benlucy/Arduino-Portable-Portrait-Painter/LiveOV7670/BufferedCameraOV7670_QQVGA_20hz_Grayscale.h

//
// Created by indrek on 30.04.2016.
//

#ifndef _BUFFEREDCAMERAOV7670_QQVGA_20HZ_GRAYSCALE_H
#define _BUFFEREDCAMERAOV7670_QQVGA_20HZ_GRAYSCALE_H

#include "BufferedCameraOV7670.h"


// 160 x 120 @ 10Hz
class BufferedCameraOV7670_QQVGA_20hz_Grayscale : public BufferedCameraOV7670<uint8_t, 160, uint8_t, 160, uint8_t, 120> {

public:
    BufferedCameraOV7670_QQVGA_20hz_Grayscale() : BufferedCameraOV7670(RESOLUTION_QQVGA_160x120, PIXEL_YUV422, 1, PLL_MULTIPLIER_X4) {};

    inline void readLine() override __attribute__((always_inline));
    void isrReadLine();

protected:
    bool setUpCamera() override;

private:
    inline void readPixels_unrolled_x160(uint16_t byteIndex) __attribute__((always_inline));
    inline void readPixels_unrolled_x10(uint16_t byteIndex) __attribute__((always_inline));
    inline void readPixel_unrolled(uint16_t byteIndex) __attribute__((always_inline));

};


volatile bool isrRead = false;
BufferedCameraOV7670_QQVGA_20hz_Grayscale * isrCamera = nullptr;



bool BufferedCameraOV7670_QQVGA_20hz_Grayscale::setUpCamera() {
  if (CameraOV7670::setUpCamera()) {
    isrCamera = this;

    *digitalPinToPCMSK(OV7670_PIXEL_CLOCK_PIN) |= bit (digitalPinToPCMSKbit(OV7670_PIXEL_CLOCK_PIN));  // enable pin
    PCICR  = 0; // disable interrupt

    return true;
  } else {
    return false;
  }
}




ISR (PCINT0_vect) { // handle pin change interrupt for D8 to D13 here
  isrCamera->isrReadLine();
  PCICR  = 0; // disable interrupt
  isrRead = false;
}


void BufferedCameraOV7670_QQVGA_20hz_Grayscale::readLine() {
  isrRead = true;
  PCIFR  |= bit(digitalPinToPCICRbit(OV7670_PIXEL_CLOCK_PIN)); // clear any outstanding interrupt
  PCICR  |= bit(digitalPinToPCICRbit(OV7670_PIXEL_CLOCK_PIN)); // enable interrupt for the group
  pixelBuffer.writeBufferPadding = 0;
  while(isrRead);
}



void BufferedCameraOV7670_QQVGA_20hz_Grayscale::isrReadLine() {
  asm volatile("nop");
  asm volatile("nop");

  // only way to get line data at 20Hz is to unroll pixel reading
  readPixels_unrolled_x160(0);
}


#define BufferedCameraOV7670_QQVGA_20hz_Grayscale_READ_PIXEL_X160_STEP 10
void BufferedCameraOV7670_QQVGA_20hz_Grayscale::readPixels_unrolled_x160(uint16_t byteIndex) {
  readPixels_unrolled_x10(byteIndex + BufferedCameraOV7670_QQVGA_20hz_Grayscale_READ_PIXEL_X160_STEP * 0);
  readPixels_unrolled_x10(byteIndex + BufferedCameraOV7670_QQVGA_20hz_Grayscale_READ_PIXEL_X160_STEP * 1);
  readPixels_unrolled_x10(byteIndex + BufferedCameraOV7670_QQVGA_20hz_Grayscale_READ_PIXEL_X160_STEP * 2);
  readPixels_unrolled_x10(byteIndex + BufferedCameraOV7670_QQVGA_20hz_Grayscale_READ_PIXEL_X160_STEP * 3);
  readPixels_unrolled_x10(byteIndex + BufferedCameraOV7670_QQVGA_20hz_Grayscale_READ_PIXEL_X160_STEP * 4);
  readPixels_unrolled_x10(byteIndex + BufferedCameraOV7670_QQVGA_20hz_Grayscale_READ_PIXEL_X160_STEP * 5);
  readPixels_unrolled_x10(byteIndex + BufferedCameraOV7670_QQVGA_20hz_Grayscale_READ_PIXEL_X160_STEP * 6);
  readPixels_unrolled_x10(byteIndex + BufferedCameraOV7670_QQVGA_20hz_Grayscale_READ_PIXEL_X160_STEP * 7);
  readPixels_unrolled_x10(byteIndex + BufferedCameraOV7670_QQVGA_20hz_Grayscale_READ_PIXEL_X160_STEP * 8);
  readPixels_unrolled_x10(byteIndex + BufferedCameraOV7670_QQVGA_20hz_Grayscale_READ_PIXEL_X160_STEP * 9);
  readPixels_unrolled_x10(byteIndex + BufferedCameraOV7670_QQVGA_20hz_Grayscale_READ_PIXEL_X160_STEP * 10);
  readPixels_unrolled_x10(byteIndex + BufferedCameraOV7670_QQVGA_20hz_Grayscale_READ_PIXEL_X160_STEP * 11);
  readPixels_unrolled_x10(byteIndex + BufferedCameraOV7670_QQVGA_20hz_Grayscale_READ_PIXEL_X160_STEP * 12);
  readPixels_unrolled_x10(byteIndex + BufferedCameraOV7670_QQVGA_20hz_Grayscale_READ_PIXEL_X160_STEP * 13);
  readPixels_unrolled_x10(byteIndex + BufferedCameraOV7670_QQVGA_20hz_Grayscale_READ_PIXEL_X160_STEP * 14);
  readPixels_unrolled_x10(byteIndex + BufferedCameraOV7670_QQVGA_20hz_Grayscale_READ_PIXEL_X160_STEP * 15);
}


void BufferedCameraOV7670_QQVGA_20hz_Grayscale::readPixels_unrolled_x10(uint16_t byteIndex) {
  readPixel_unrolled(byteIndex + 0);
  readPixel_unrolled(byteIndex + 1);
  readPixel_unrolled(byteIndex + 2);
  readPixel_unrolled(byteIndex + 3);
  readPixel_unrolled(byteIndex + 4);
  readPixel_unrolled(byteIndex + 5);
  readPixel_unrolled(byteIndex + 6);
  readPixel_unrolled(byteIndex + 7);
  readPixel_unrolled(byteIndex + 8);
  readPixel_unrolled(byteIndex + 9);
}

void BufferedCameraOV7670_QQVGA_20hz_Grayscale::readPixel_unrolled(uint16_t byteIndex) {
  readPixelByte(pixelBuffer.writeBuffer[byteIndex]);
  asm volatile("nop");
}








#endif //_BUFFEREDCAMERAOV7670_QQVGA_20HZ_GRAYSCALE_H
