benlucy/Arduino-Portable-Portrait-Painter/LiveOV7670/GrayScaleTable.h

//
// Created by indrek on 1.12.2016.
//

#ifndef LIVEOV7670_GRAYSCALETABLE_H
#define LIVEOV7670_GRAYSCALETABLE_H




const uint8_t graysScaleTableHigh[] = {
    0x00,
    0x00,
    0x00,
    0x00,
    0x00,
    0x00,
    0x00,
    0x00,
    0x08,
    0x08,
    0x08,
    0x08,
    0x08,
    0x08,
    0x08,
    0x08,
    0x10,
    0x10,
    0x10,
    0x10,
    0x10,
    0x10,
    0x10,
    0x10,
    0x18,
    0x18,
    0x18,
    0x18,
    0x18,
    0x18,
    0x18,
    0x18,
    0x21,
    0x21,
    0x21,
    0x21,
    0x21,
    0x21,
    0x21,
    0x21,
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
};



uint8_t graysScaleTableLow[] = {
    0x00,
    0x00,
    0x00,
    0x00,
    0x20,
    0x20,
    0x20,
    0x20,
    0x41,
    0x41,
    0x41,
    0x41,
    0x61,
    0x61,
    0x61,
    0x61,
    0x82,
    0x82,
    0x82,
    0x82,
    0xA2,
    0xA2,
    0xA2,
    0xA2,
    0xC3,
    0xC3,
    0xC3,
    0xC3,
    0xE3,
    0xE3,
    0xE3,
    0xE3,
    0x04,
    0x04,
    0x04,
    0x04,
    0x24,
    0x24,
    0x24,
    0x24,
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
};




#endif //LIVEOV7670_GRAYSCALETABLE_H
